AntonioVillanuevaSegura/Baliza_Arduino_cw/DOC/photo_2026-01-31_19-09-05 (2).jpg

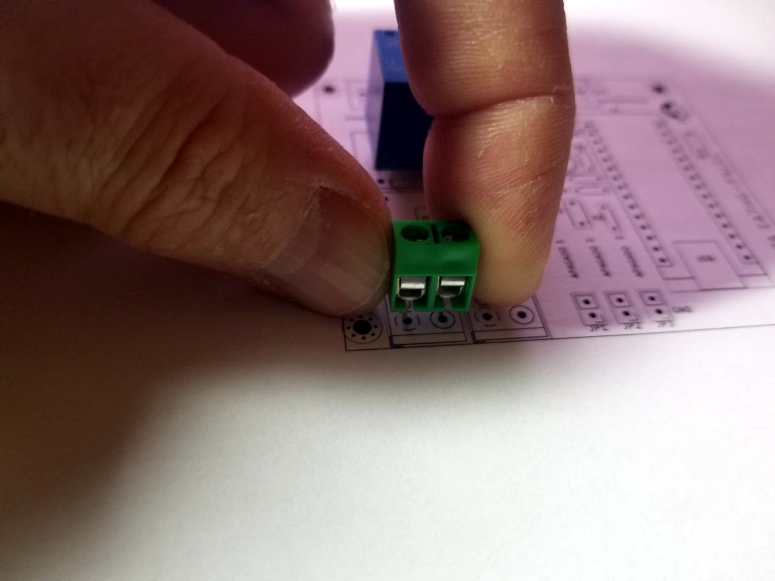
DOC/photo_2026-01-31_19-09-05 (2).jpg
