AntonioVillanuevaSegura/Baliza_Arduino_cw/fotos/photo_2026-02-13_18-31-22 (2).jpg

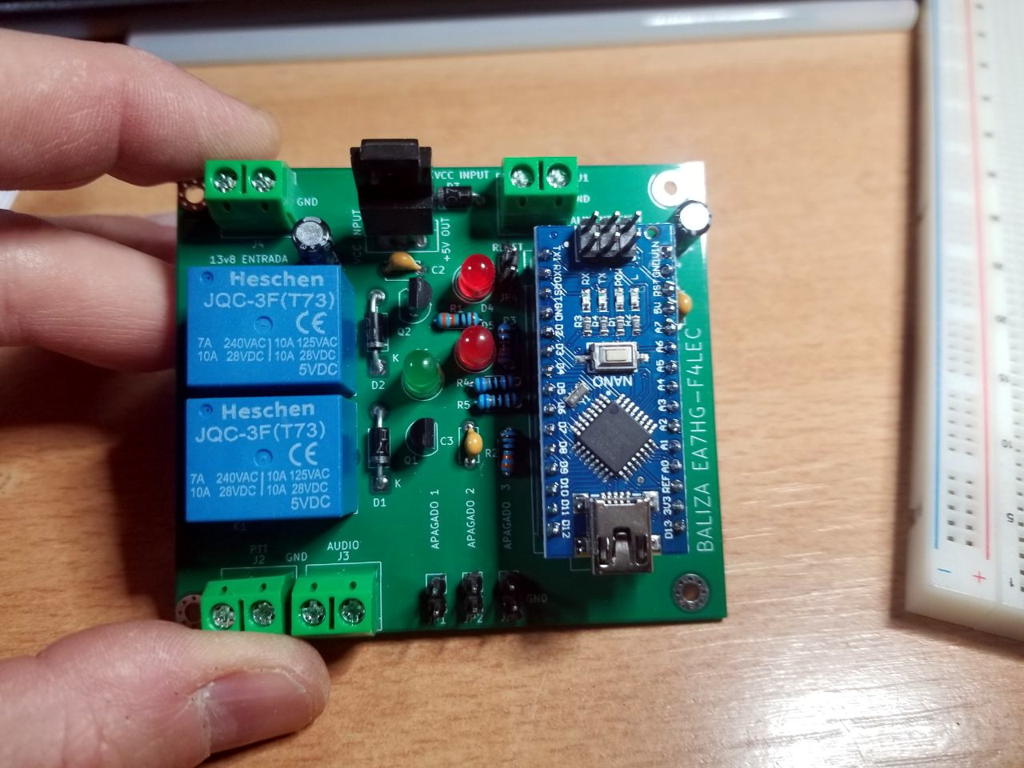
fotos/photo_2026-02-13_18-31-22 (2).jpg
