AntonioVillanuevaSegura/Baliza_Arduino_cw/fotos/photo_2026-02-14_14-58-19 (3).jpg

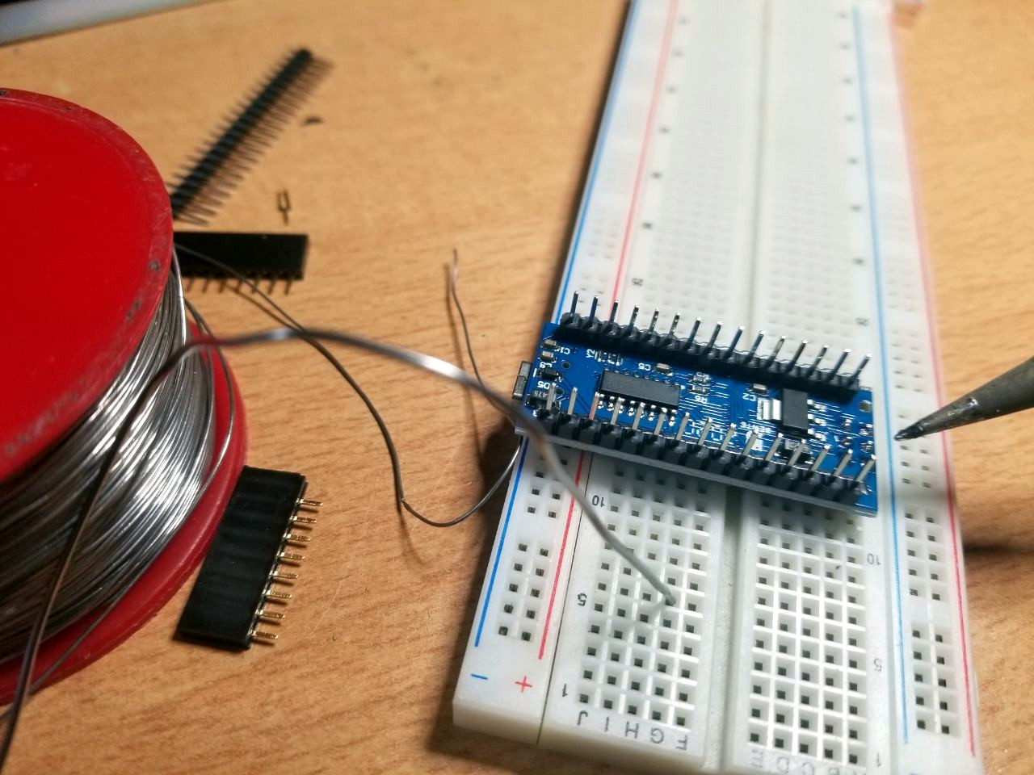
fotos/photo_2026-02-14_14-58-19 (3).jpg
